cfbender/Lubrigante/case_layouts/ergosaurus/angled/L5.dxf

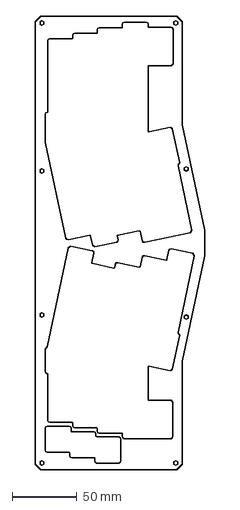
[picture p15: CAD file, 2020-01-24]
case_layouts/ergosaurus/angled/L5.dxf
130.3 x 348.8 mm
