cfbender/Lubrigante/case_layouts/ergosaurus/flat-front/L5.dxf

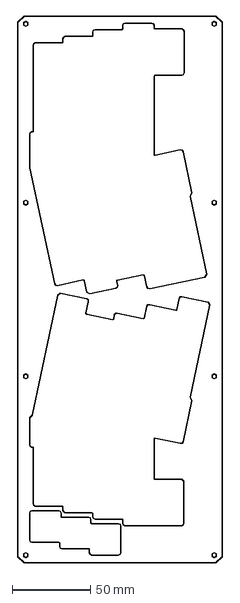
[picture p16: CAD file, 2020-01-20]
case_layouts/ergosaurus/flat-front/L5.dxf
130.3 x 348.8 mm
