cfbender/Lubrigante/case_layouts/ergosaurus/angled/L0.dxf

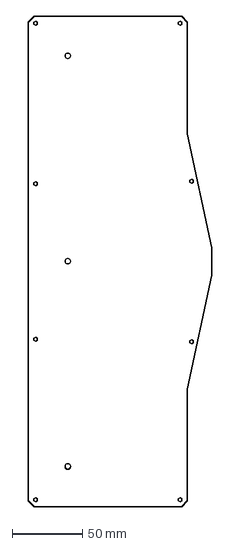
[picture p17: CAD file, 2020-01-24]
case_layouts/ergosaurus/angled/L0.dxf
130.3 x 348.8 mm
