cfbender/Lubrigante/case_layouts/ergosaurus/flat-front/L6.dxf

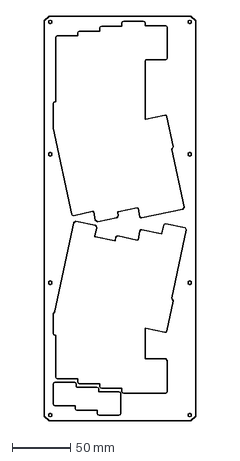
[picture p18: CAD file, 2020-01-20]
case_layouts/ergosaurus/flat-front/L6.dxf
130.2 x 348.8 mm
