cfbender/Lubrigante/case_layouts/ergosaurus/angled/L1.dxf

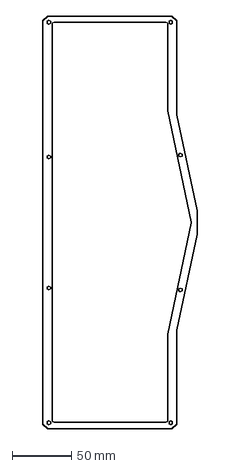
[picture p19: CAD file, 2020-01-24]
case_layouts/ergosaurus/angled/L1.dxf
130.3 x 348.8 mm
